SteveMayze/lps-1/doc/PanelLayout.pdf

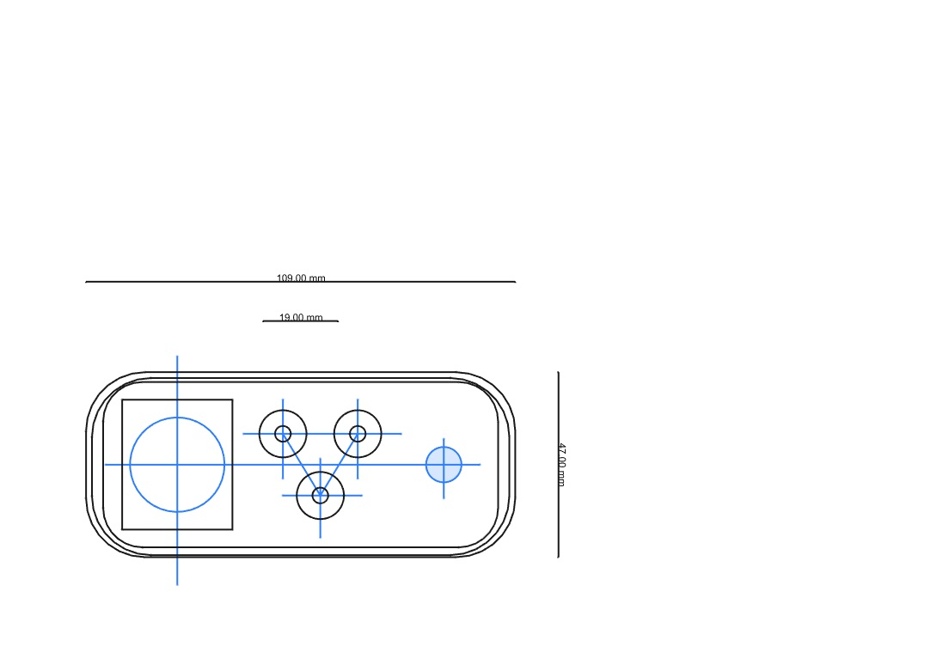
[picture p3: page 1]
