SteveMayze/lps-1/doc/ConfigurationBits.png

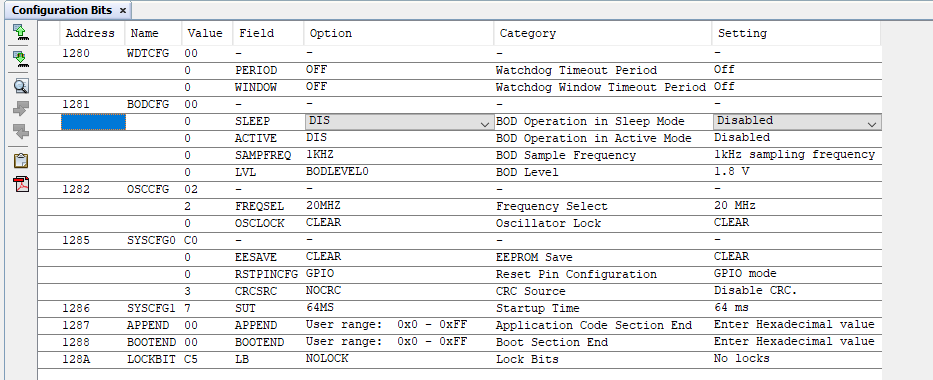
doc/ConfigurationBits.png
