SteveMayze/lps-1/doc/Connection_bb2.png

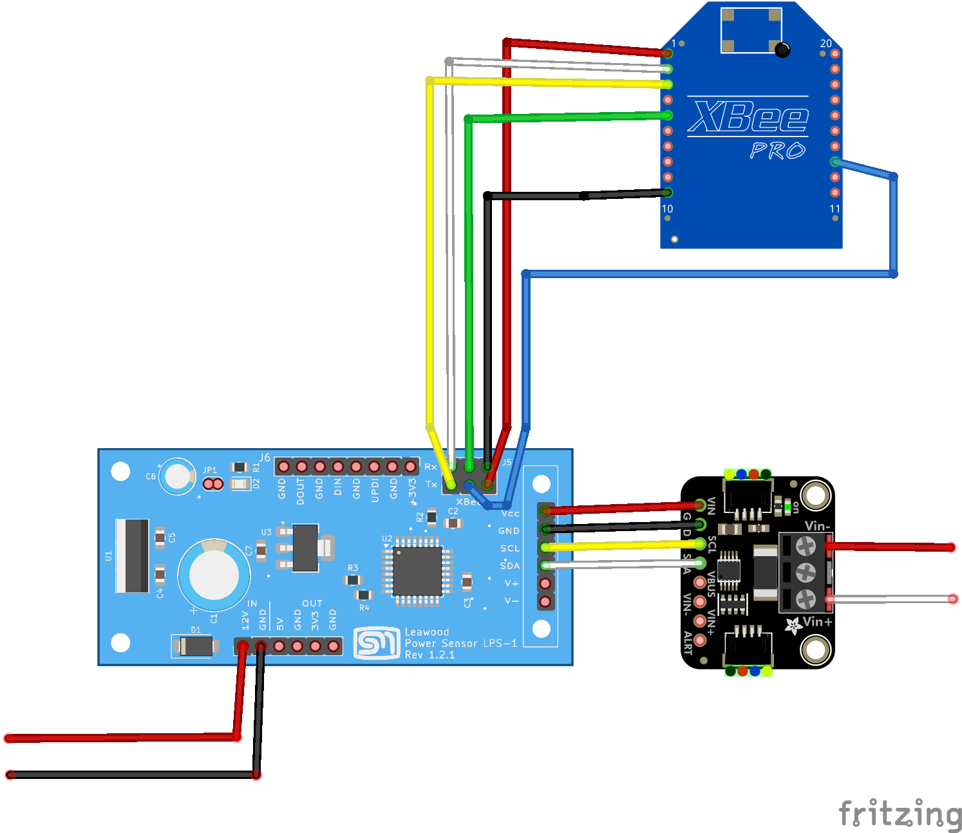
doc/Connection_bb2.png
