SteveMayze/lps-1/doc/Connection_bb.png

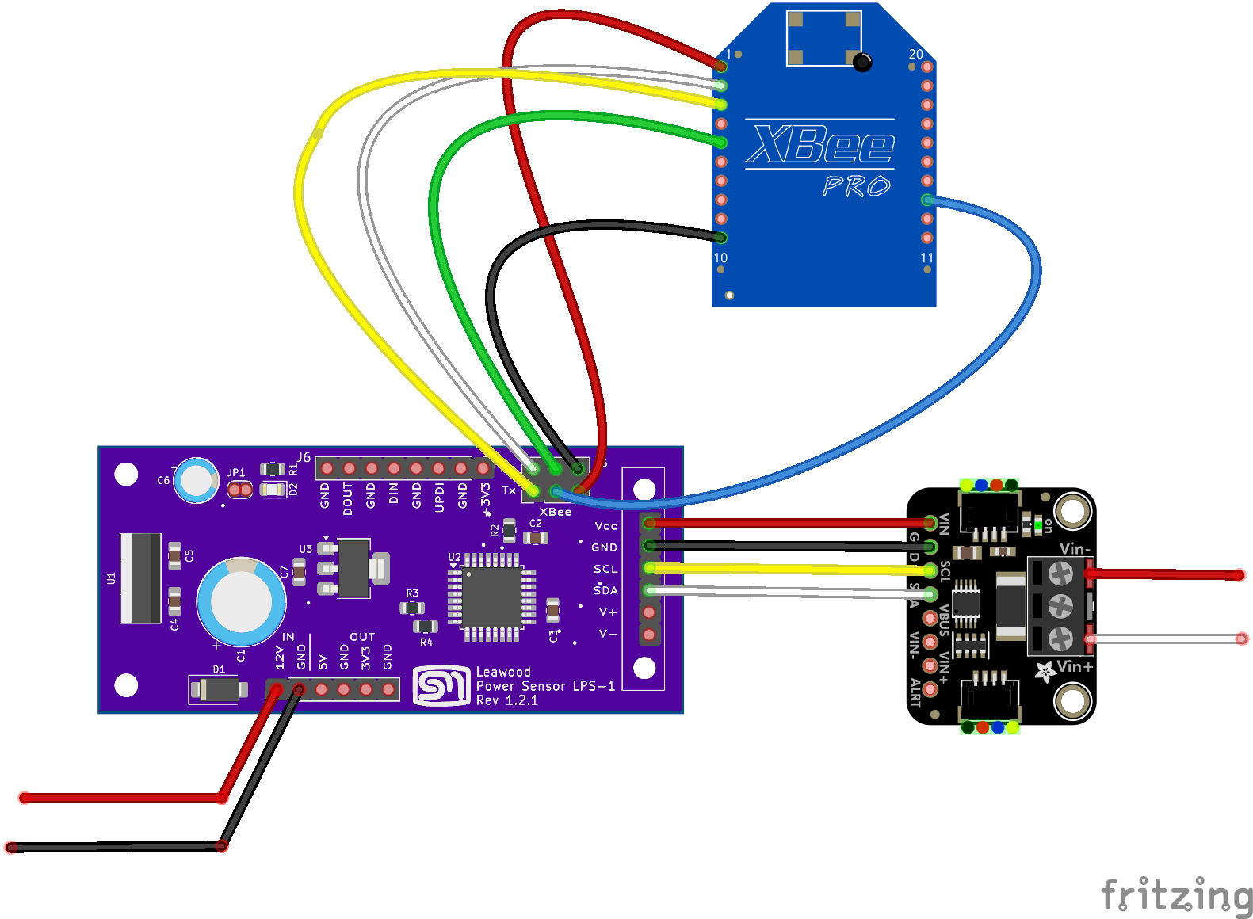
doc/Connection_bb.png
