SteveMayze/lps-1/doc/PowerCircuit.png

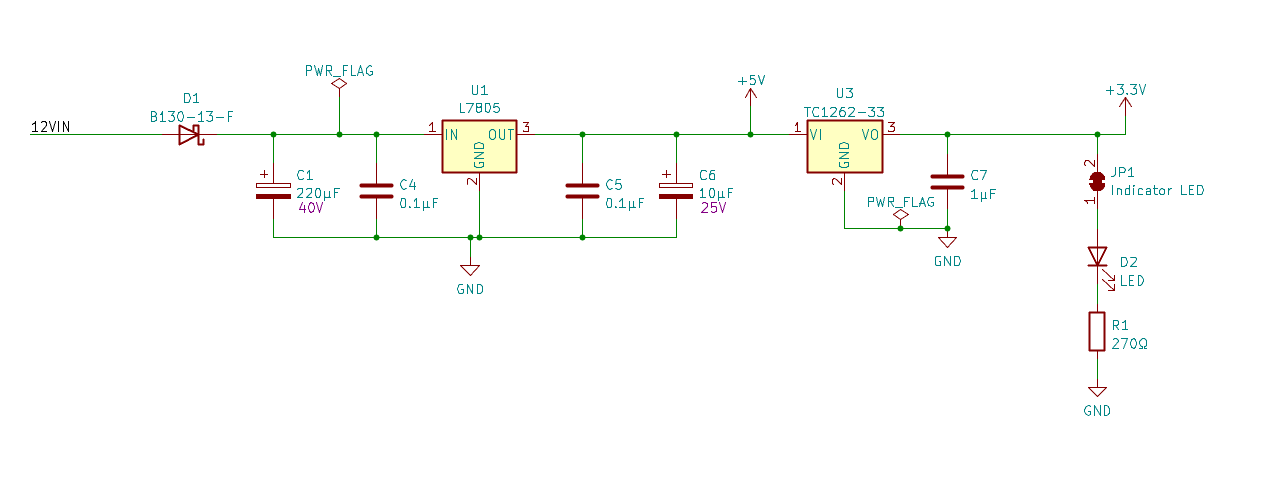
doc/PowerCircuit.png
