SteveMayze/lps-1/doc/AsseblyTest.png

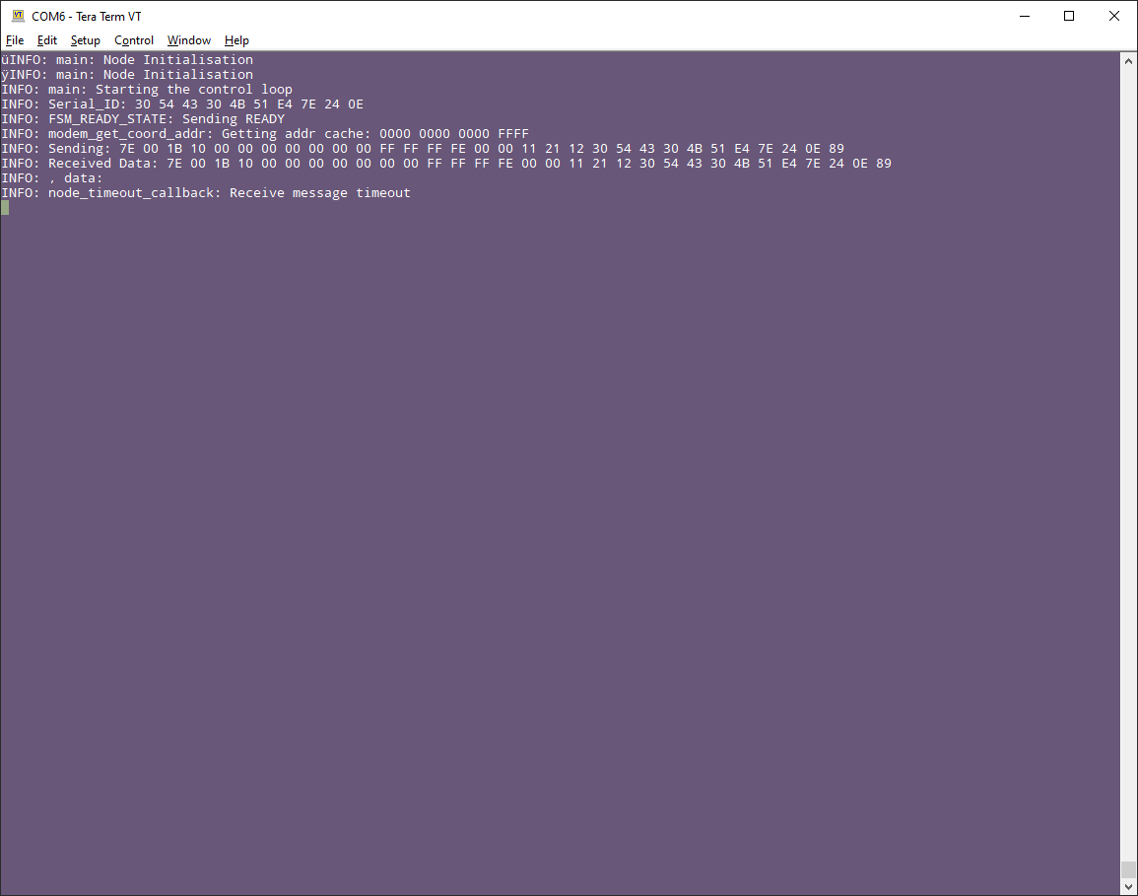
doc/AsseblyTest.png
