SteveMayze/lps-1/doc/lps-1.pdf

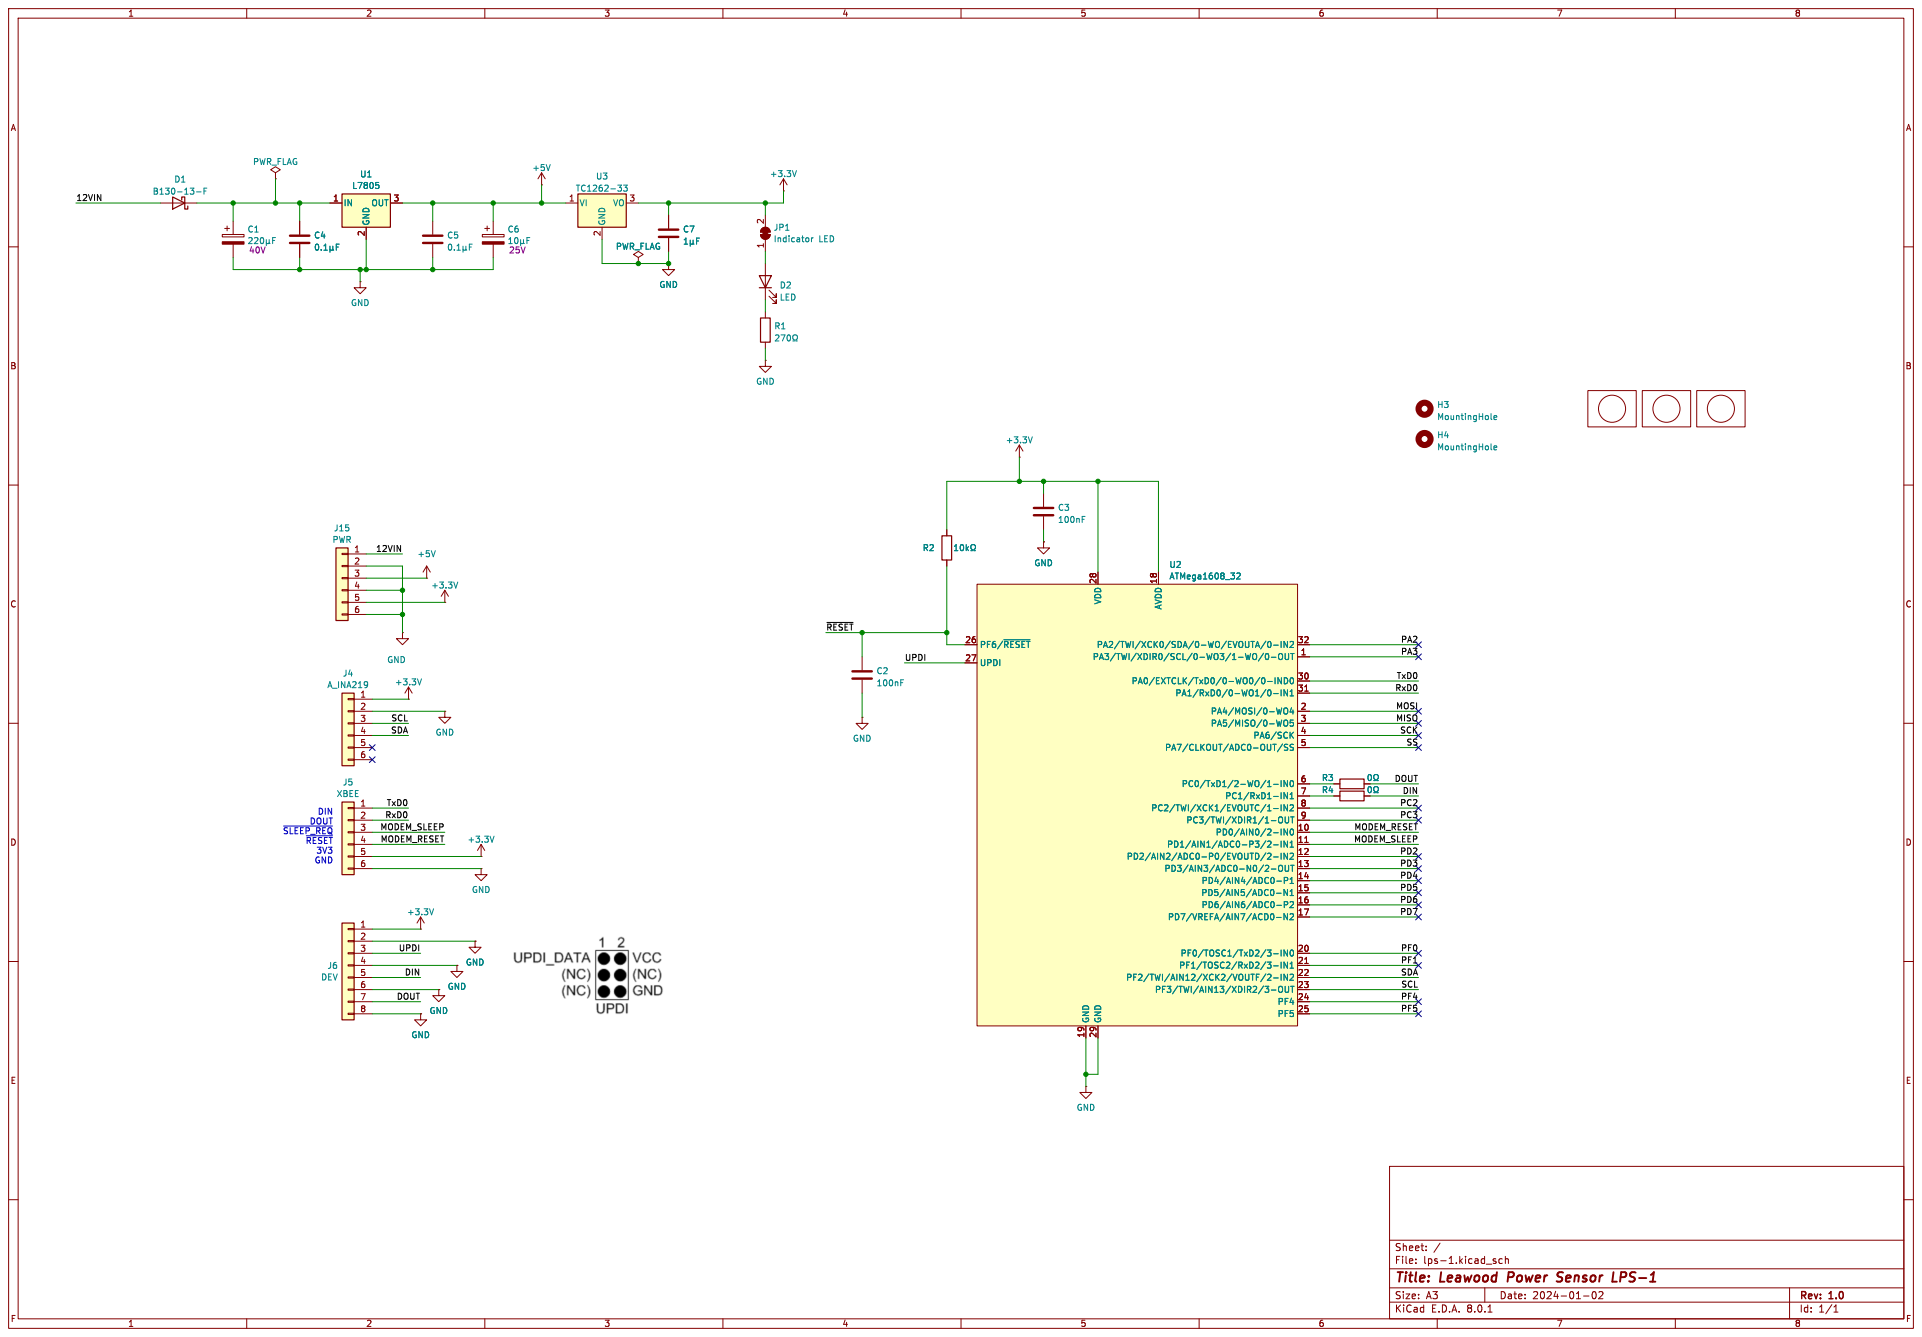
[picture p31: page 1]

File: lps-1.kicad_sch Sheet: /
Id: 1/1 Title: Leawood Power Sensor LPS-1
