SteveMayze/lps-1/doc/Fischer-Curve.pdf

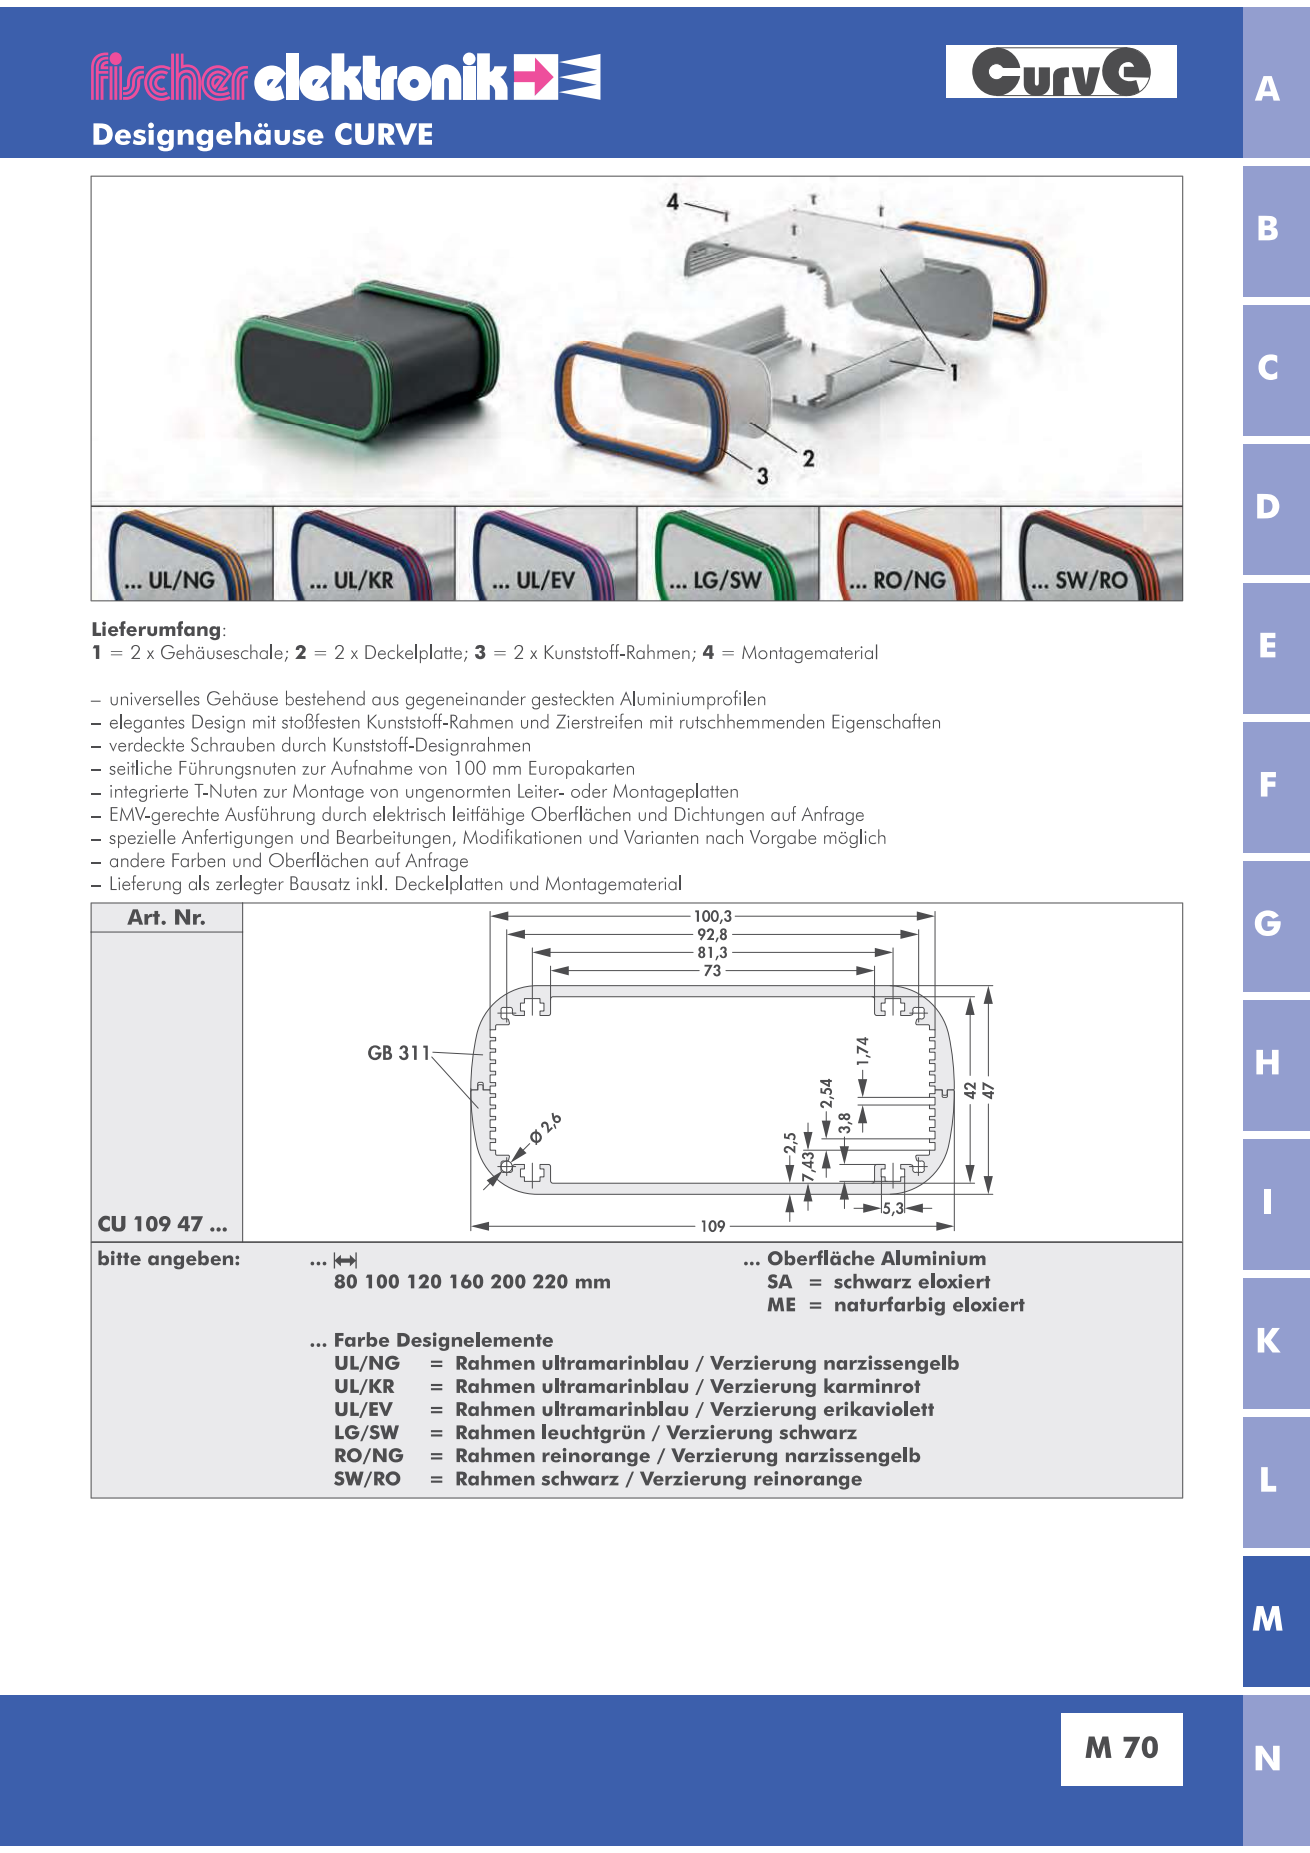
[picture p32: page 1]
