SteveMayze/lps-1/doc/RJ45_CHBUA_VE_DB.pdf

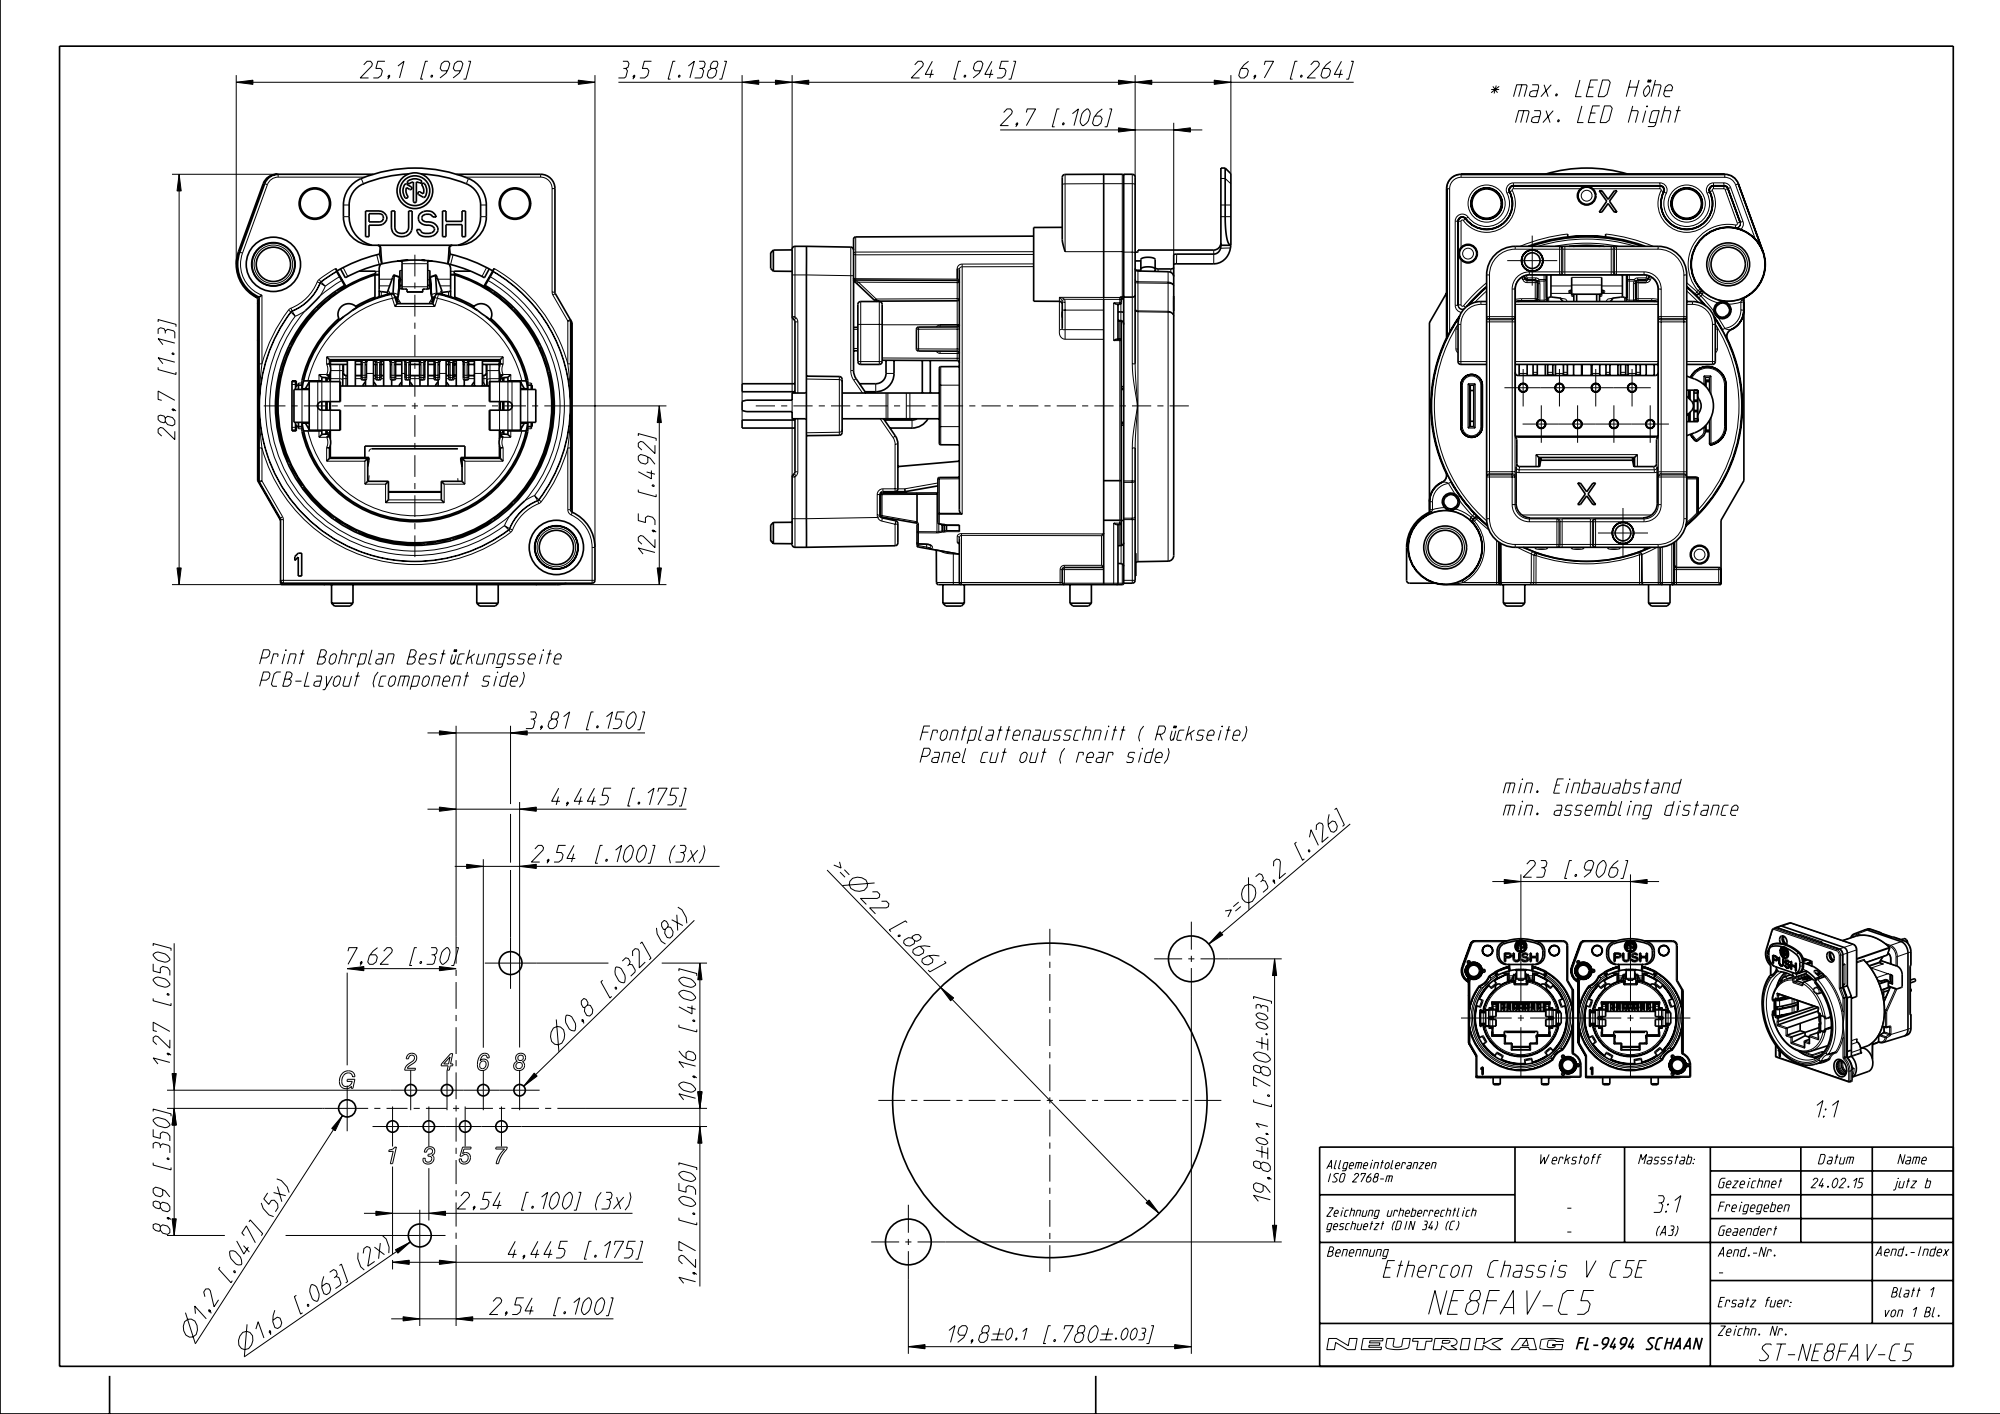
[picture p33: page 1]
