SteveMayze/lps-1/doc/Artwork-Front.pdf

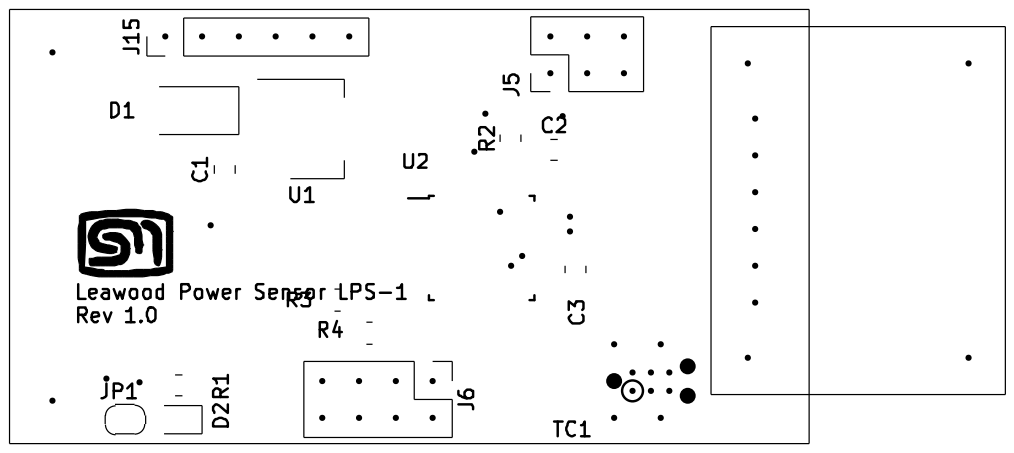
[picture p34: page 1]
